Stormpegy/dancepad/electronics/img/IMG_20200415_173844.jpg

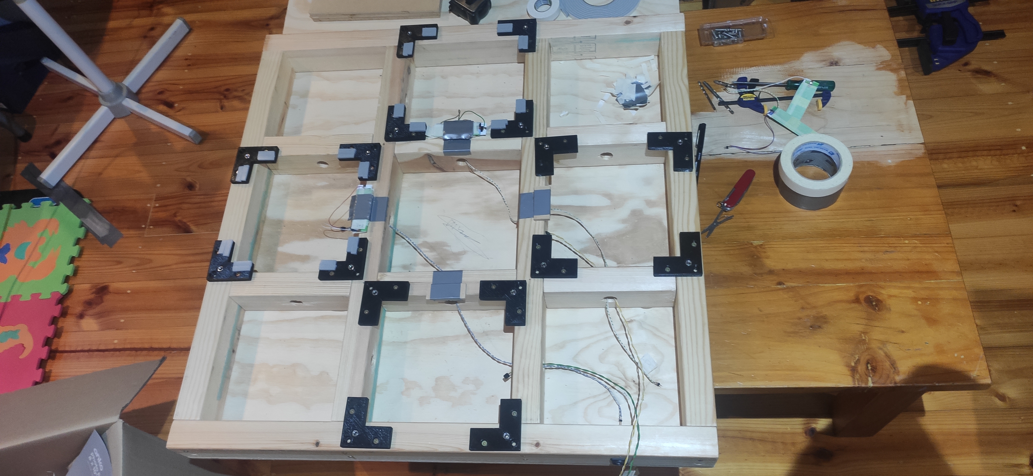
electronics/img/IMG_20200415_173844.jpg
