Stormpegy/dancepad/electronics/img/IMG_20200617_214602.jpg

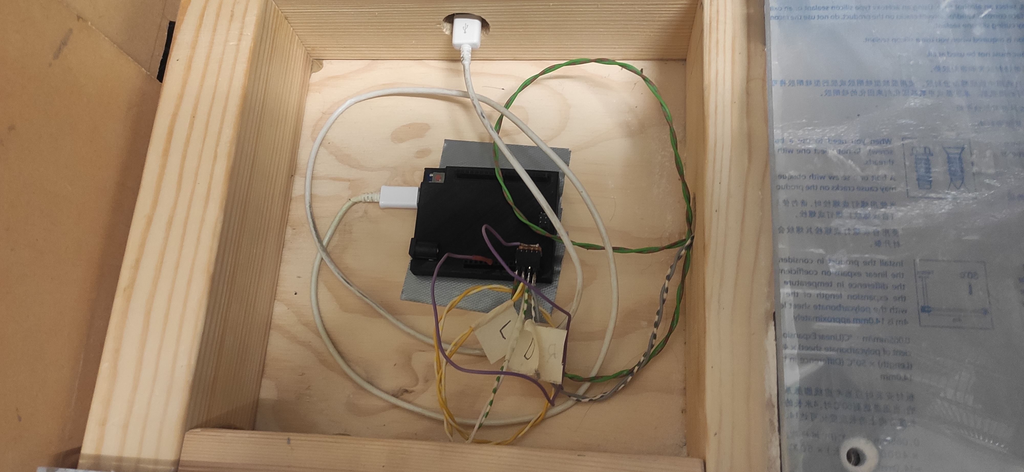
electronics/img/IMG_20200617_214602.jpg
