Stormpegy/dancepad/frame/img/IMG_20200329_193702.jpg

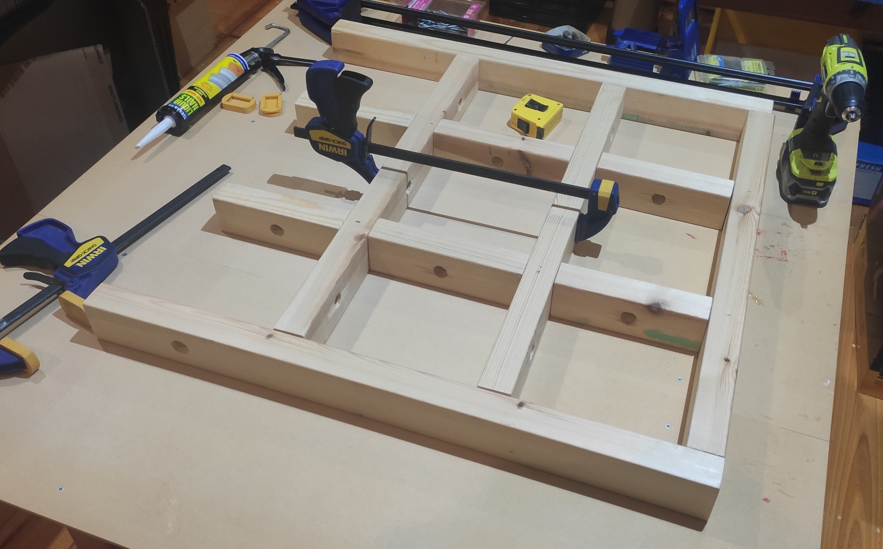
frame/img/IMG_20200329_193702.jpg
