Stormpegy/dancepad/panels/img/IMG_20200419_134314.jpg

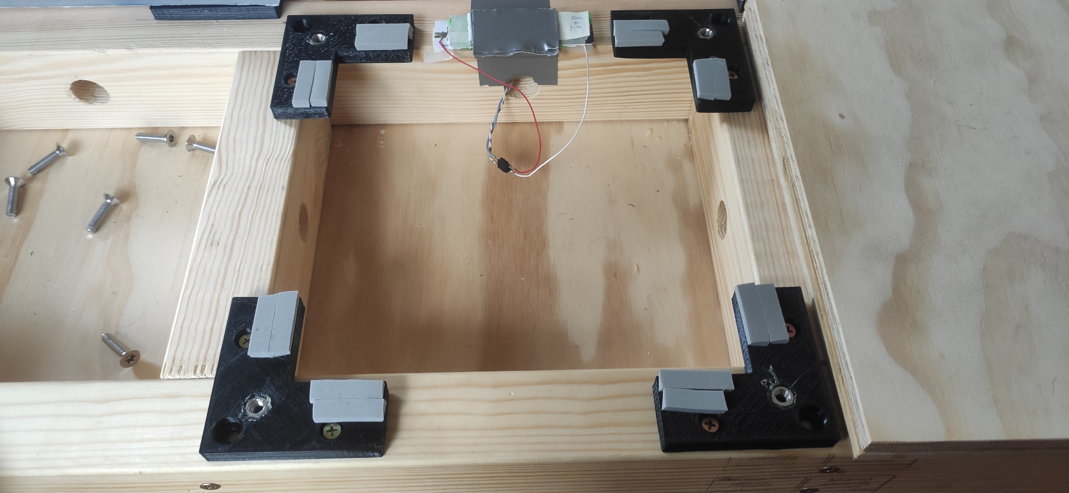
panels/img/IMG_20200419_134314.jpg
